pestvillian/ASAT/Dorjee/usb_AND_touchscreen/Utilities/Media/Pictures/JPG/Photo4.jpg

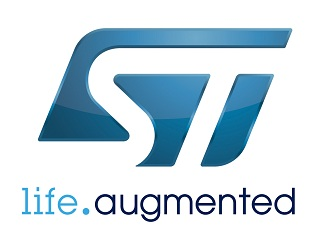
Dorjee/usb_AND_touchscreen/Utilities/Media/Pictures/JPG/Photo4.jpg
