pestvillian/ASAT/Dorjee/usb_AND_touchscreen/Utilities/Media/Pictures/BMP_480x272/image04.bmp

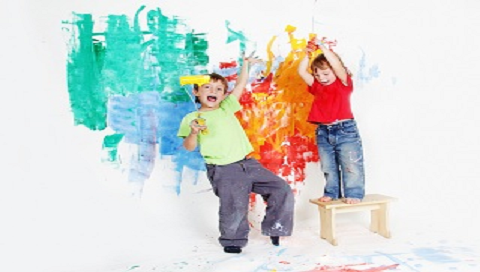
Dorjee/usb_AND_touchscreen/Utilities/Media/Pictures/BMP_480x272/image04.bmp
