pestvillian/ASAT/Dorjee/usb_AND_touchscreen/Utilities/Media/Pictures/BMP_128x160/3_16.bmp

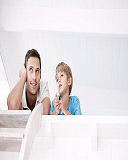
Dorjee/usb_AND_touchscreen/Utilities/Media/Pictures/BMP_128x160/3_16.bmp
