pestvillian/ASAT/Dorjee/usb_AND_touchscreen/Utilities/Media/Pictures/BMP_240x240/16-bits/image05.bmp

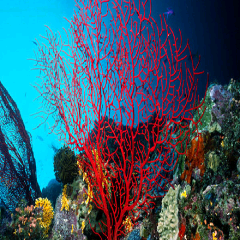
Dorjee/usb_AND_touchscreen/Utilities/Media/Pictures/BMP_240x240/16-bits/image05.bmp
