pestvillian/ASAT/Dorjee/usb_AND_touchscreen/Utilities/Media/Pictures/BMP_240x320/2.bmp

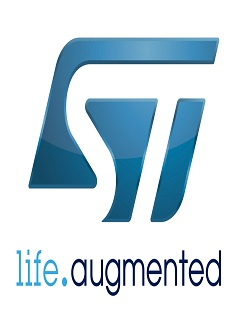
Dorjee/usb_AND_touchscreen/Utilities/Media/Pictures/BMP_240x320/2.bmp
