pestvillian/ASAT/Dorjee/usb_AND_touchscreen/Utilities/Media/Pictures/BMP_240x320/13.bmp

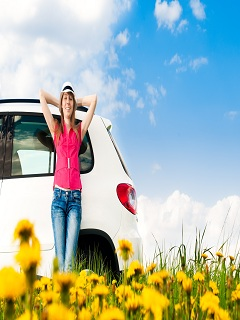
Dorjee/usb_AND_touchscreen/Utilities/Media/Pictures/BMP_240x320/13.bmp
