pestvillian/ASAT/Dorjee/usb_AND_touchscreen/Utilities/Media/Pictures/BMP_240x320/14.bmp

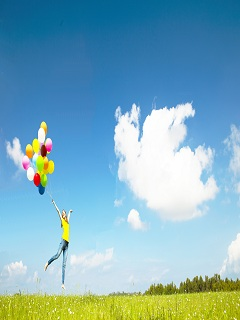
Dorjee/usb_AND_touchscreen/Utilities/Media/Pictures/BMP_240x320/14.bmp
