pestvillian/ASAT/Dorjee/usb_AND_touchscreen/Utilities/Media/Pictures/JPG/Photo1.jpg

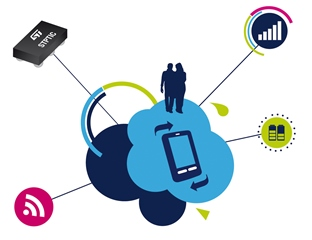
Dorjee/usb_AND_touchscreen/Utilities/Media/Pictures/JPG/Photo1.jpg
