pestvillian/ASAT/Dorjee/usb_AND_touchscreen/Utilities/Media/Pictures/JPG/Photo3.jpg

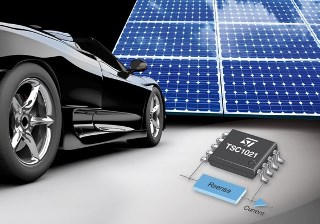
Dorjee/usb_AND_touchscreen/Utilities/Media/Pictures/JPG/Photo3.jpg
