pestvillian/ASAT/Dorjee/usb_AND_touchscreen/Utilities/Media/Pictures/JPG/Photo6.jpg

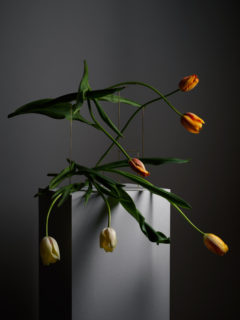
Dorjee/usb_AND_touchscreen/Utilities/Media/Pictures/JPG/Photo6.jpg
