pestvillian/ASAT/Greg/esp32-c6-devkitc-1-pin-layout.png

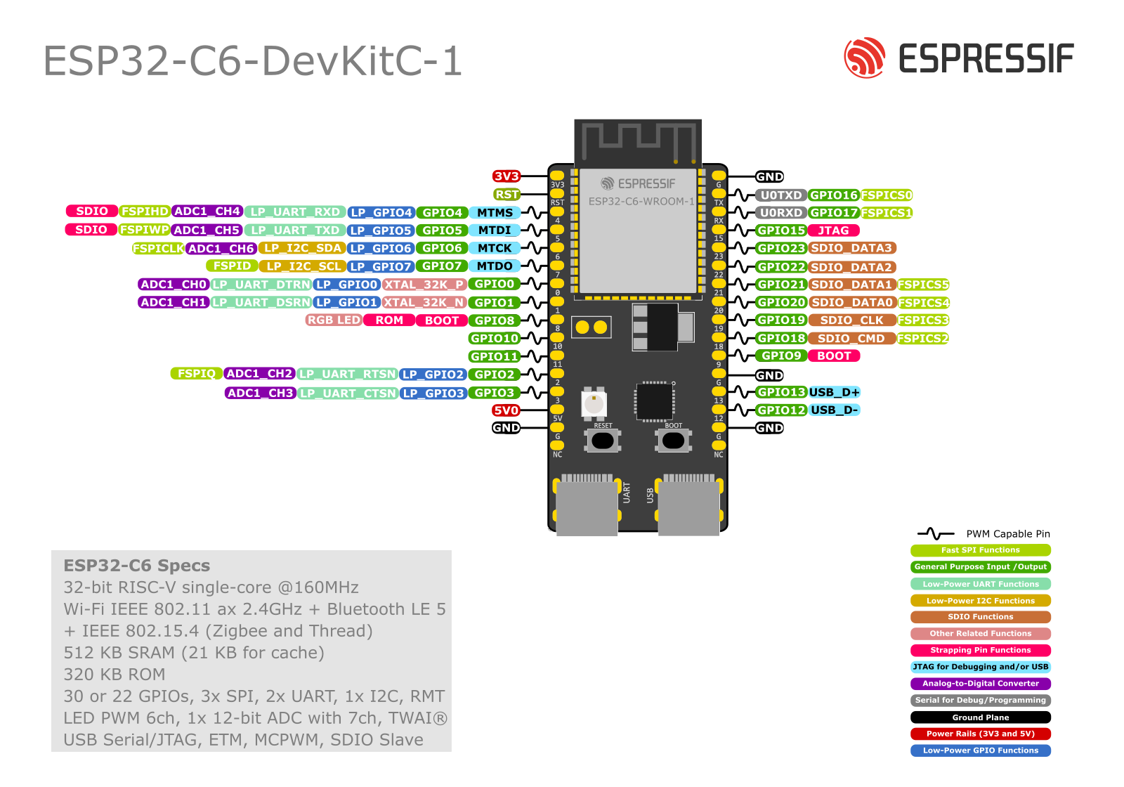
Greg/esp32-c6-devkitc-1-pin-layout.png
