pestvillian/ASAT/Greg/Prototype/Temp_directory/whora_the_explora.png

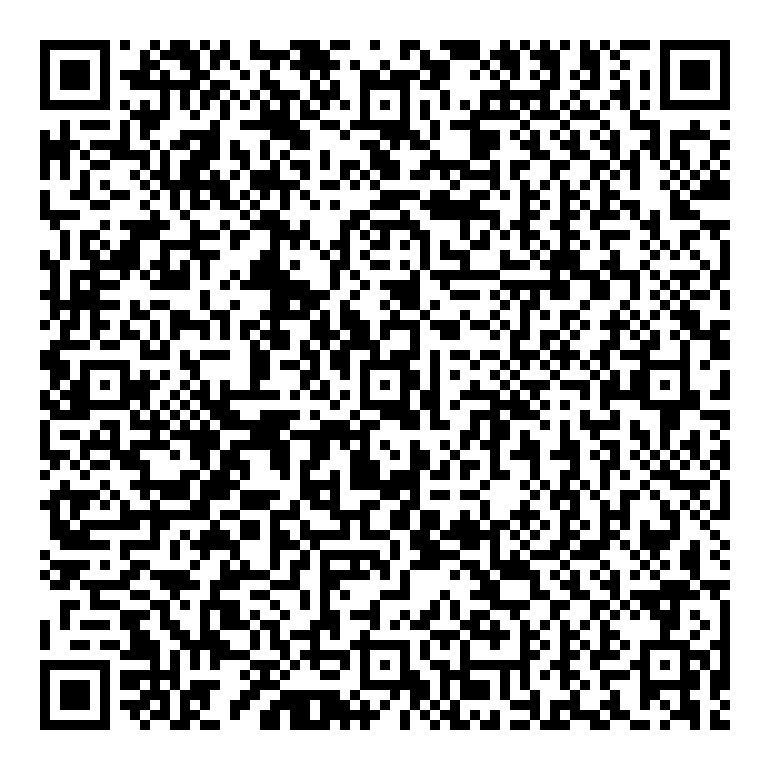
Greg/Prototype/Temp_directory/whora_the_explora.png
