pestvillian/ASAT/Greg/3DPrints-Exports/PrimaryBodyV9WLM.4.2.stl

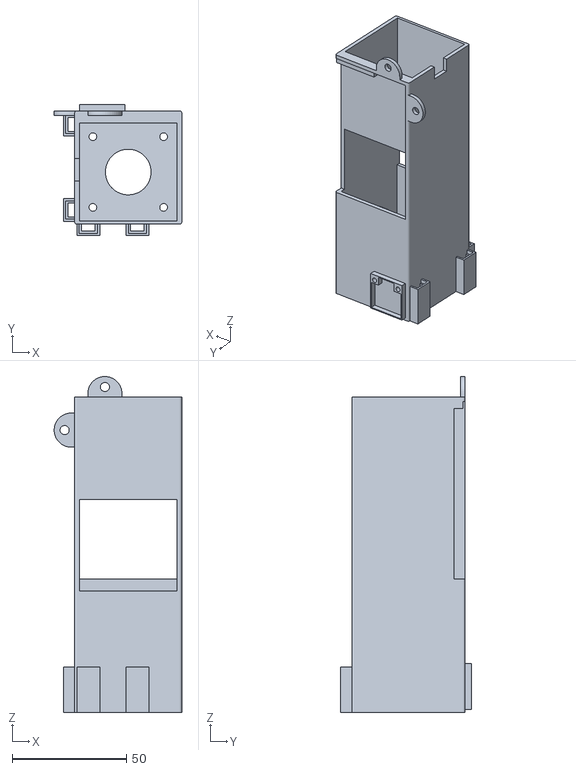
[picture p53: CAD file, 2025-05-20]
Greg/3DPrints-Exports/PrimaryBodyV9WLM.4.2.stl
56.0 x 57.5 x 147.3
