pestvillian/ASAT/Motor_Controller_Board/Motor_Controller_Board/Screw Terminal Block 5mm 2-way.step

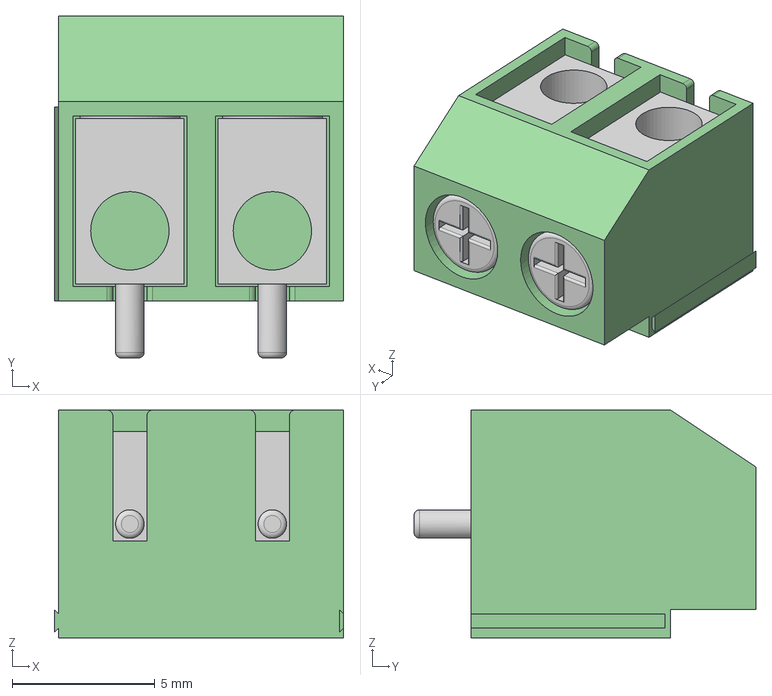
[picture p54: CAD file, 2025-05-06]
Motor_Controller_Board/Motor_Controller_Board/Screw Terminal Block 5mm 2-way.step
10.2 x 12.0 x 8.00 mm
