pestvillian/ASAT/Greg/KVgui/q.test3_QR.png

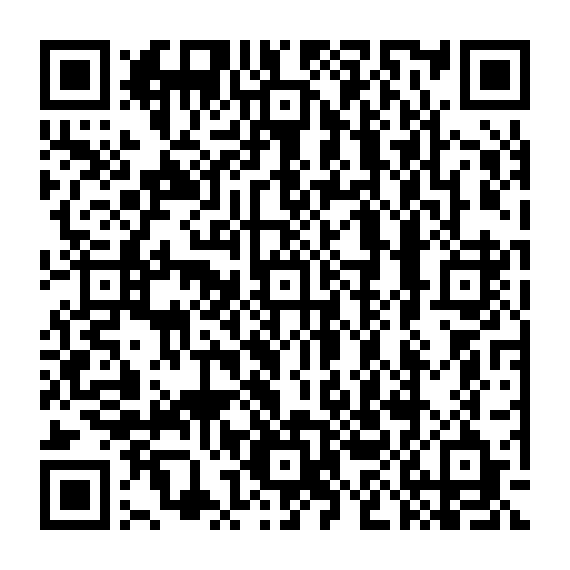
Greg/KVgui/q.test3_QR.png
