pestvillian/ASAT/Dorjee/useful_screenshots/flash-memory-debugger/multi-line-protocols/prot1.png

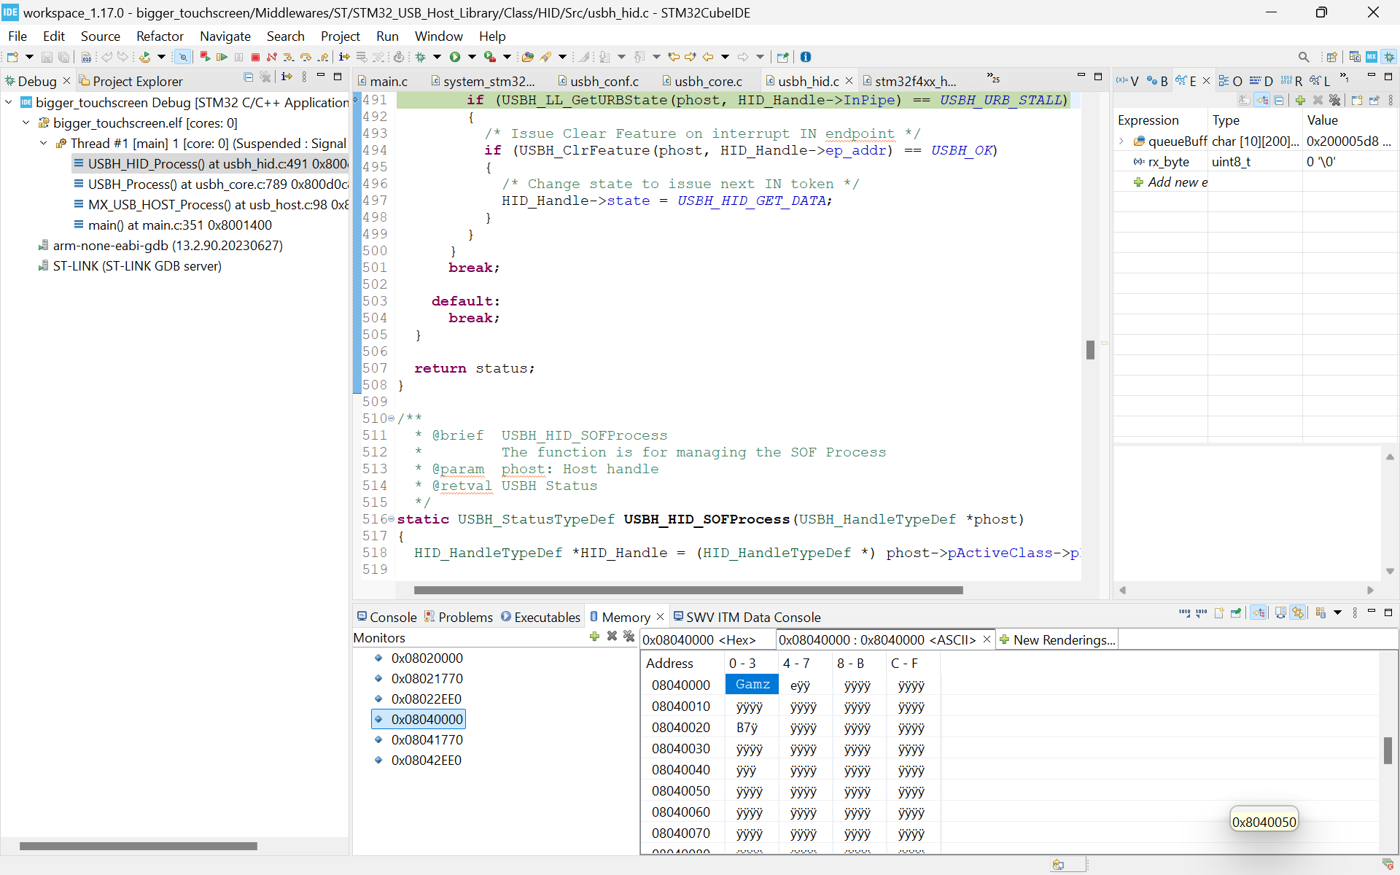
Dorjee/useful_screenshots/flash-memory-debugger/multi-line-protocols/prot1.png
