pestvillian/ASAT/Dorjee/useful_screenshots/flash-memory-debugger/one-line-protocols/prot1.png

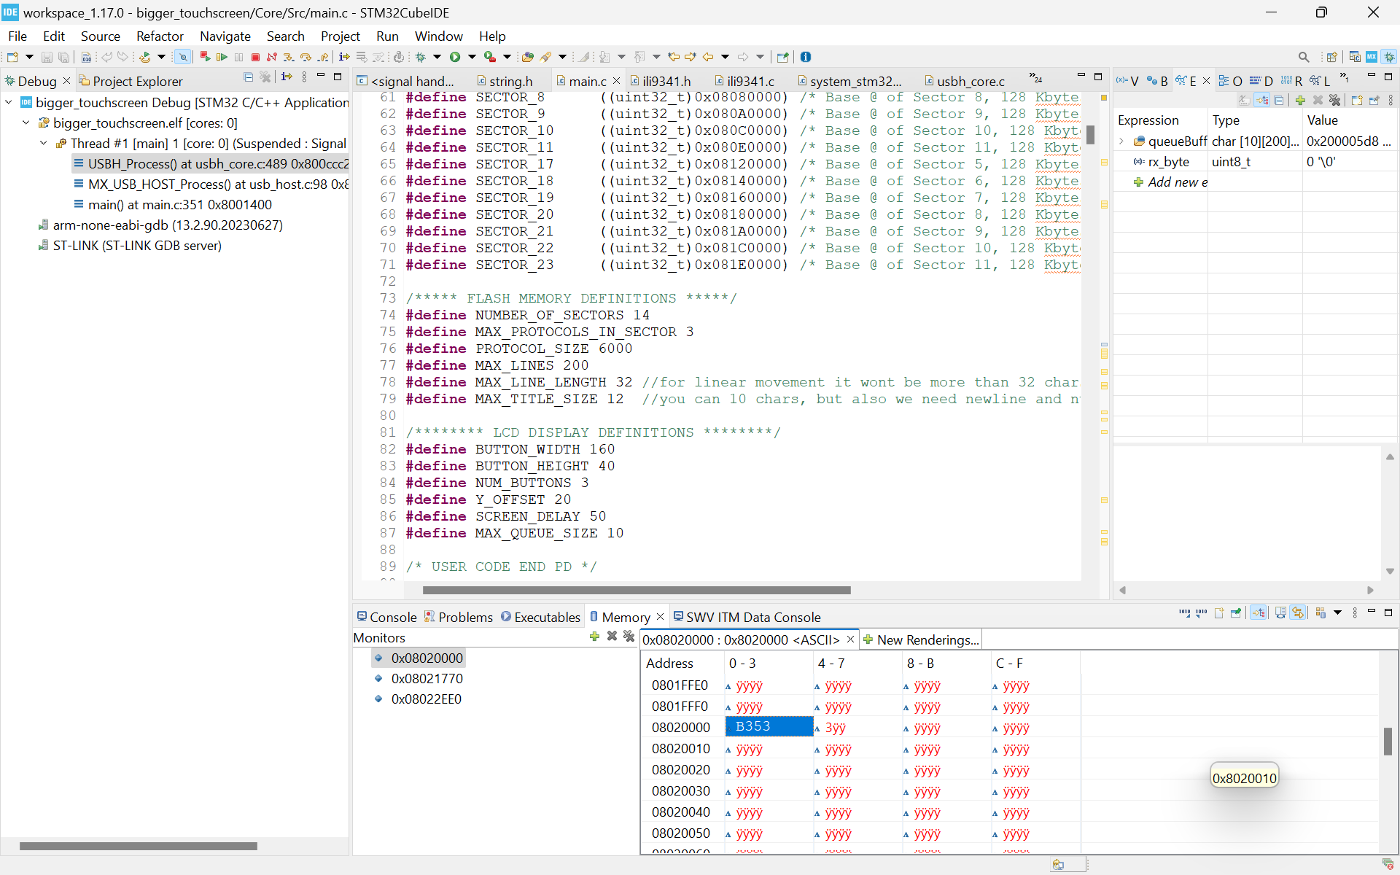
Dorjee/useful_screenshots/flash-memory-debugger/one-line-protocols/prot1.png
